acobley/SiliconMind/SiliconMind/Tests/TurnONSwitchLeds/TurnONSwitchLeds.ino

#include "SPI.h"

boolean LED1 =false;
int count=0;
int ENOUT=7;
int DAOUT=1;
int DBOUT=0;
int A0OUT=4;
int A1OUT=5;
int A2OUT=6;

void writeOut(){
  

  digitalWrite(DBOUT,true);

  digitalWrite(A2OUT,true);
  digitalWrite(A1OUT,false);
  digitalWrite(A0OUT,false);
  

  
}

void setup() {
  // put your setup code here, to run once:
  LED1=true;
  pinMode(ENOUT,OUTPUT);
  pinMode(DAOUT,OUTPUT);
  pinMode(DBOUT,OUTPUT);
  pinMode(A0OUT,OUTPUT);
  pinMode(A1OUT,OUTPUT);
  pinMode(A2OUT,OUTPUT);
  digitalWrite(ENOUT,true);
}



void loop() {
  // put your main code here, to run repeatedly:
  
  writeOut();
  

}
